seanboyce/Calculus-the-game/calculus_full/unpowered.JPG

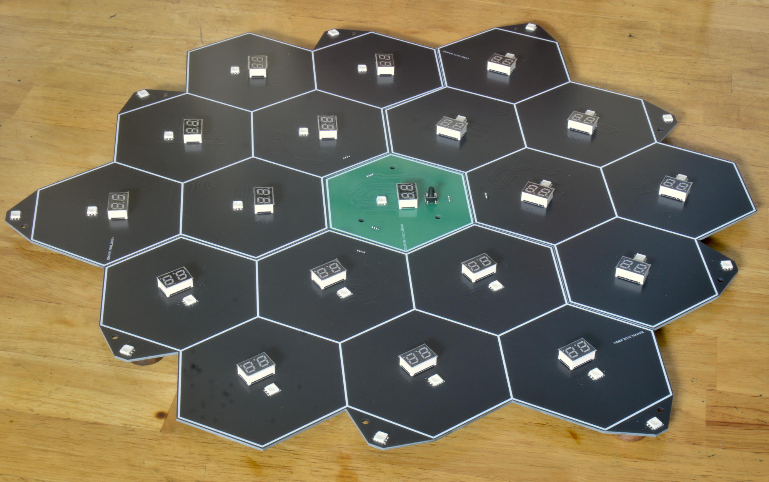
calculus_full/unpowered.JPG
